helmarw/yarh.io-mods/Pictures/IMG_6970.jpg

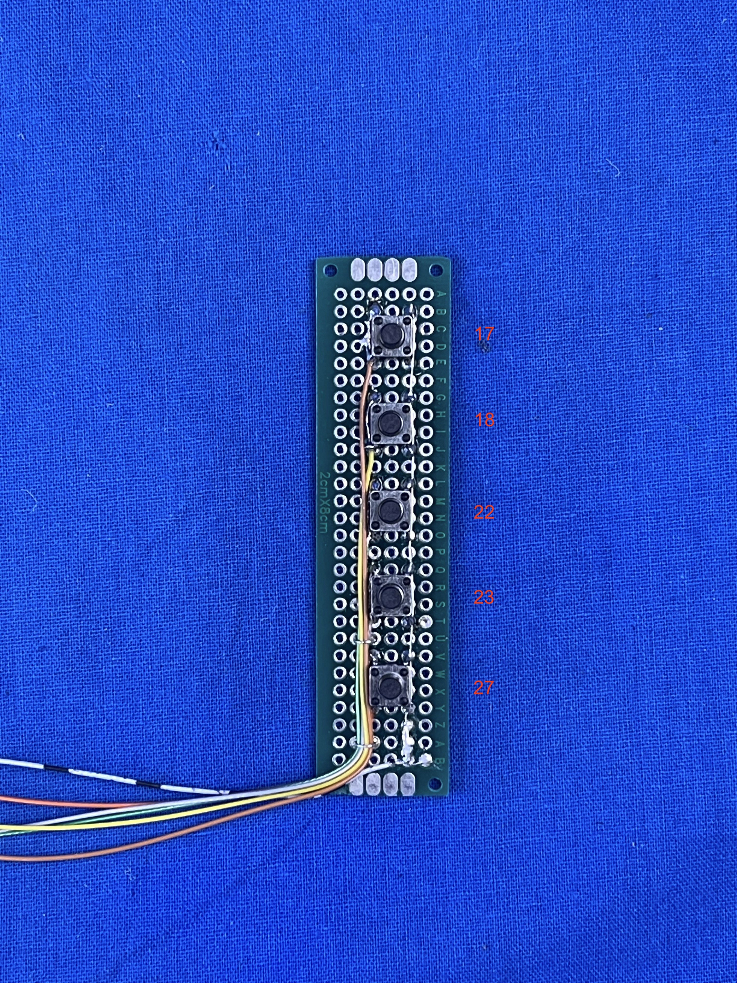
Pictures/IMG_6970.jpg
