helmarw/yarh.io-mods/Pictures/IMG_6971.jpg

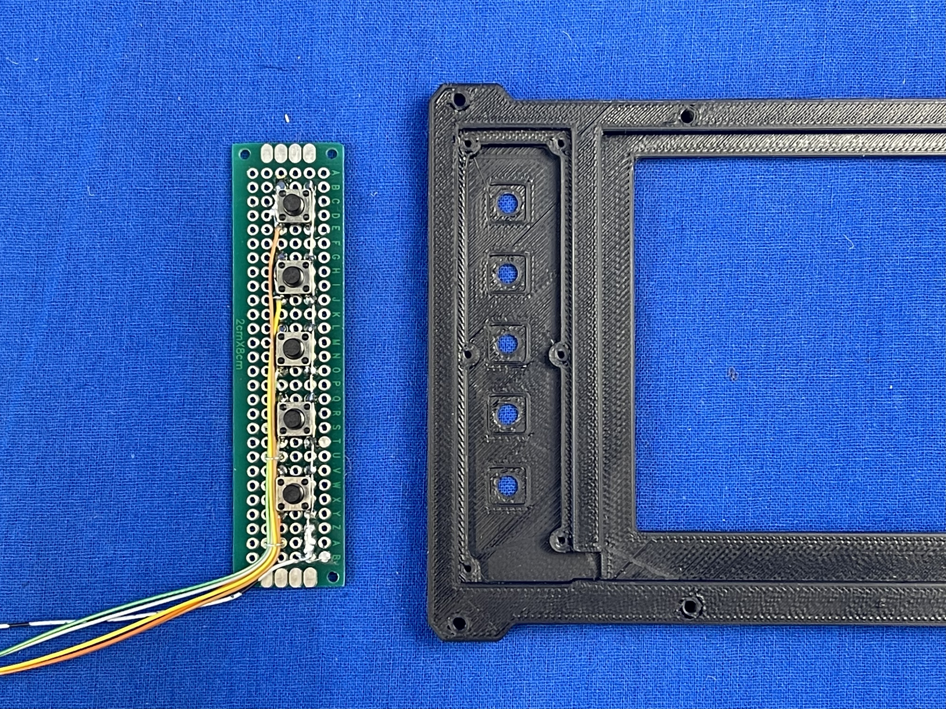
Pictures/IMG_6971.jpg
