helmarw/yarh.io-mods/Pictures/IMG_6976.jpg

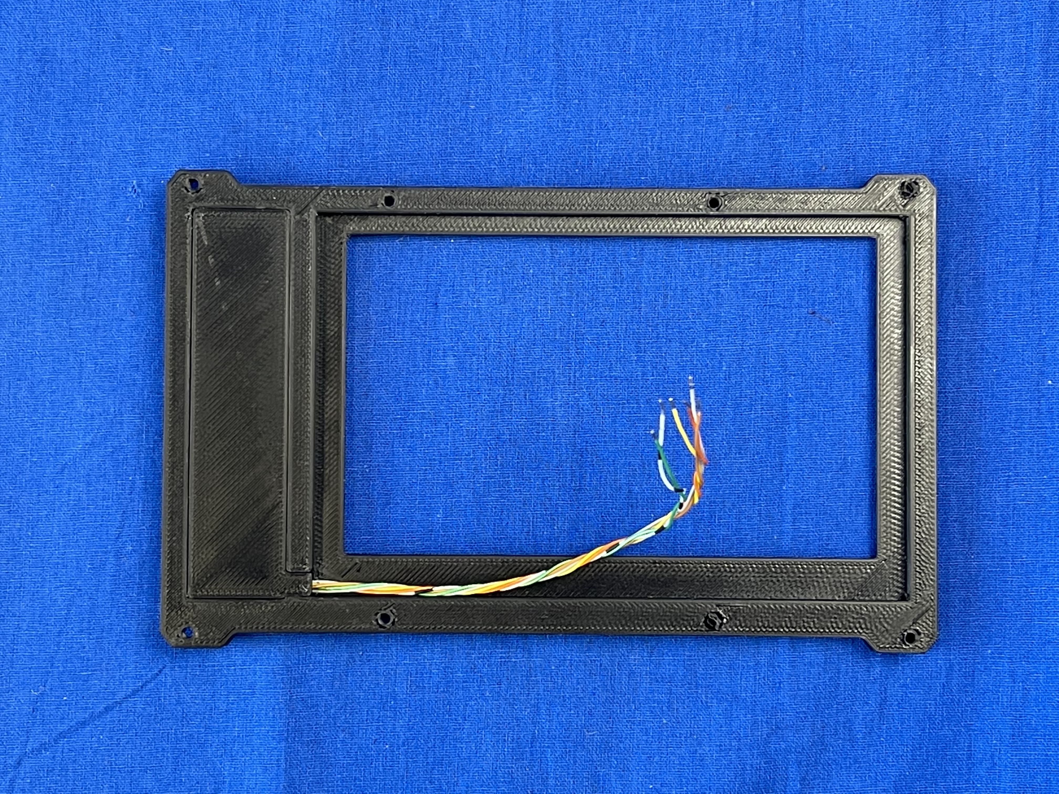
Pictures/IMG_6976.jpg
