helmarw/yarh.io-mods/Pictures/IMG_6977.jpg

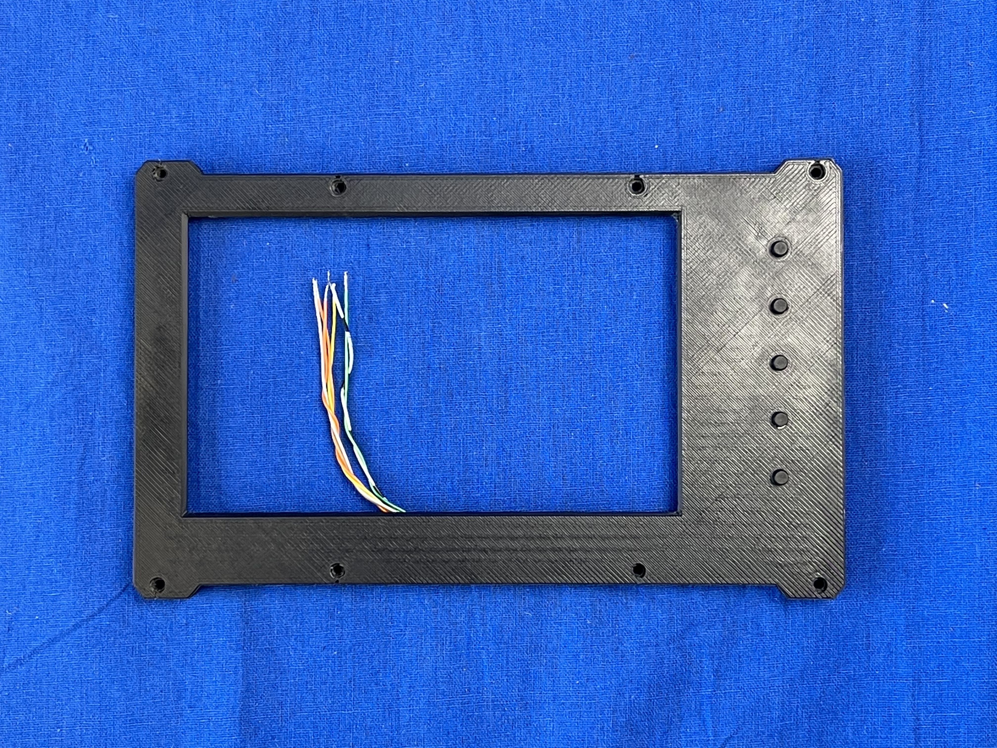
Pictures/IMG_6977.jpg
