helmarw/yarh.io-mods/Pictures/IMG_6978.jpg

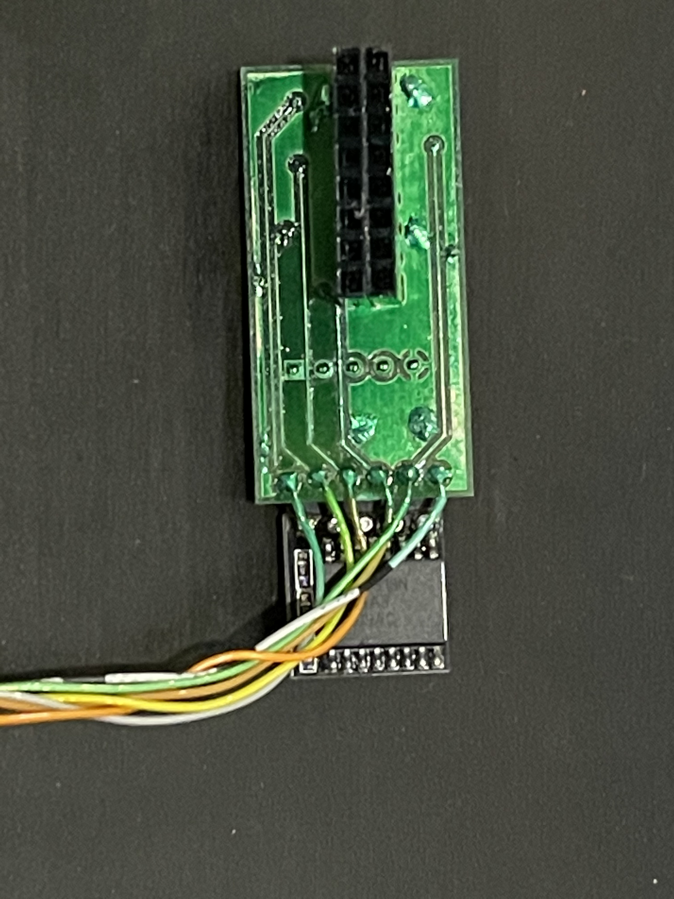
Pictures/IMG_6978.jpg
