helmarw/yarh.io-mods/Pictures/IMG_6979.jpg

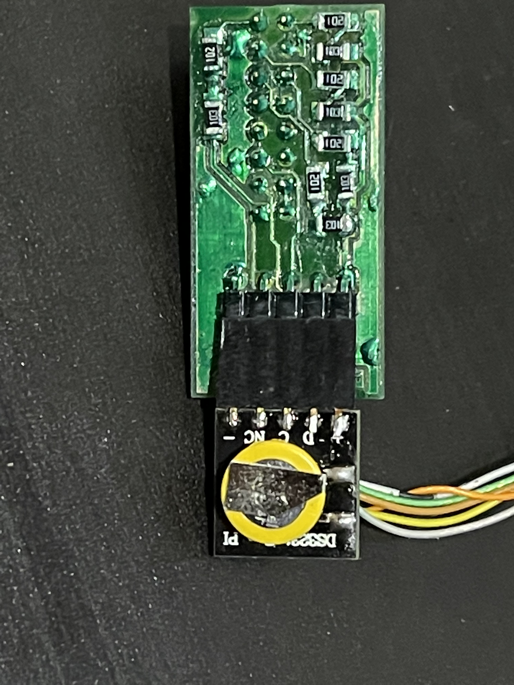
Pictures/IMG_6979.jpg
