helmarw/yarh.io-mods/Pictures/IMG_6972.jpg

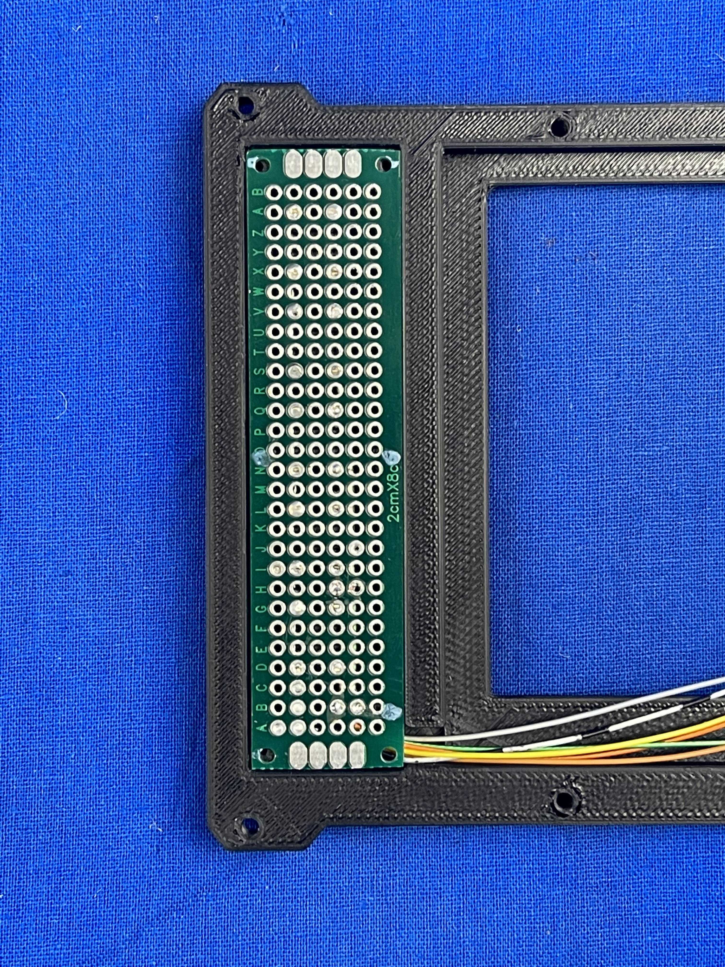
Pictures/IMG_6972.jpg
